RockBase-iot/NM-EPD-420/src/ui/epd_uc8179_420c.cpp

#include "epd_uc8179_420c.h"

static inline uint8_t remapPlaneData(uint8_t command, uint8_t data)
{
    return (command == 0x13) ? static_cast<uint8_t>(~data) : data;
}

GxEPD2_420c_NM_UC8179::GxEPD2_420c_NM_UC8179(int16_t cs, int16_t dc, int16_t rst, int16_t busy)
    : GxEPD2_EPD(cs, dc, rst, busy, LOW, 25000000, WIDTH, HEIGHT,
                 panel, hasColor, hasPartialUpdate, hasFastPartialUpdate)
{
}

void GxEPD2_420c_NM_UC8179::clearScreen(uint8_t value) { clearScreen(value, 0xFF); }

void GxEPD2_420c_NM_UC8179::clearScreen(uint8_t black_value, uint8_t color_value)
{
    writeScreenBuffer(black_value, color_value);
    refresh(false);
}

void GxEPD2_420c_NM_UC8179::writeScreenBuffer(uint8_t value) { writeScreenBuffer(value, 0xFF); }

void GxEPD2_420c_NM_UC8179::writeScreenBuffer(uint8_t black_value, uint8_t color_value)
{
    if (!_init_display_done) _InitDisplay();
    _writeScreenBuffer(0x10, black_value);
    _writeScreenBuffer(0x13, color_value);
    _initial_write = false;
}

void GxEPD2_420c_NM_UC8179::_writeScreenBuffer(uint8_t command, uint8_t value)
{
    _setPartialRamArea(0, 0, WIDTH, HEIGHT);
    _writeCommand(command);
    _startTransfer();
    uint8_t tx = remapPlaneData(command, value);
    for (uint32_t i = 0; i < uint32_t(WIDTH) * uint32_t(HEIGHT) / 8; i++) _transfer(tx);
    _endTransfer();
}

void GxEPD2_420c_NM_UC8179::writeImage(const uint8_t bitmap[], int16_t x, int16_t y,
                                       int16_t w, int16_t h, bool invert, bool mirror_y, bool pgm)
{
    _writeScreenBuffer(0x13, 0xFF);
    _writeImage(0x10, bitmap, x, y, w, h, invert, mirror_y, pgm);
}

void GxEPD2_420c_NM_UC8179::_writeImage(uint8_t command, const uint8_t bitmap[],
                                        int16_t x, int16_t y, int16_t w, int16_t h,
                                        bool invert, bool mirror_y, bool pgm)
{
    if (_initial_write) writeScreenBuffer();
    delay(1);
    uint16_t wb = (w + 7) / 8;
    x -= x % 8;
    w = wb * 8;
    int16_t x1 = x < 0 ? 0 : x;
    int16_t y1 = y < 0 ? 0 : y;
    int16_t w1 = x + w < int16_t(WIDTH) ? w : int16_t(WIDTH) - x;
    int16_t h1 = y + h < int16_t(HEIGHT) ? h : int16_t(HEIGHT) - y;
    int16_t dx = x1 - x;
    int16_t dy = y1 - y;
    w1 -= dx;
    h1 -= dy;
    if ((w1 <= 0) || (h1 <= 0)) return;
    if (!_init_display_done) _InitDisplay();
    _writeCommand(0x91);
    _setPartialRamArea(x1, y1, w1, h1);
    _writeCommand(command);
    _startTransfer();
    for (int16_t i = 0; i < h1; i++) {
        for (int16_t j = 0; j < w1 / 8; j++) {
            uint16_t idx = mirror_y
                ? j + dx / 8 + uint16_t((h - 1 - (i + dy))) * wb
                : j + dx / 8 + uint16_t(i + dy) * wb;
            uint8_t data = pgm ? pgm_read_byte(&bitmap[idx]) : bitmap[idx];
            if (invert) data = ~data;
            _transfer(remapPlaneData(command, data));
        }
    }
    _endTransfer();
    _writeCommand(0x92);
    delay(1);
}

void GxEPD2_420c_NM_UC8179::writeImagePart(const uint8_t bitmap[],
        int16_t x_part, int16_t y_part, int16_t w_bitmap, int16_t h_bitmap,
        int16_t x, int16_t y, int16_t w, int16_t h, bool invert, bool mirror_y, bool pgm)
{
    _writeImagePart(0x10, bitmap, x_part, y_part, w_bitmap, h_bitmap, x, y, w, h,
                    invert, mirror_y, pgm);
}

void GxEPD2_420c_NM_UC8179::_writeImagePart(uint8_t command, const uint8_t bitmap[],
        int16_t x_part, int16_t y_part, int16_t w_bitmap, int16_t h_bitmap,
        int16_t x, int16_t y, int16_t w, int16_t h, bool invert, bool mirror_y, bool pgm)
{
    if (_initial_write) writeScreenBuffer();
    delay(1);
    if ((w_bitmap < 0) || (h_bitmap < 0) || (w < 0) || (h < 0)) return;
    if ((x_part < 0) || (x_part >= w_bitmap)) return;
    if ((y_part < 0) || (y_part >= h_bitmap)) return;
    uint16_t wb_bitmap = (w_bitmap + 7) / 8;
    x_part -= x_part % 8;
    w = w_bitmap - x_part < w ? w_bitmap - x_part : w;
    h = h_bitmap - y_part < h ? h_bitmap - y_part : h;
    x -= x % 8;
    w = 8 * ((w + 7) / 8);
    int16_t x1 = x < 0 ? 0 : x;
    int16_t y1 = y < 0 ? 0 : y;
    int16_t w1 = x + w < int16_t(WIDTH) ? w : int16_t(WIDTH) - x;
    int16_t h1 = y + h < int16_t(HEIGHT) ? h : int16_t(HEIGHT) - y;
    int16_t dx = x1 - x;
    int16_t dy = y1 - y;
    w1 -= dx;
    h1 -= dy;
    if ((w1 <= 0) || (h1 <= 0)) return;
    if (!_init_display_done) _InitDisplay();
    _writeCommand(0x91);
    _setPartialRamArea(x1, y1, w1, h1);
    _writeCommand(command);
    _startTransfer();
    for (int16_t i = 0; i < h1; i++) {
        for (int16_t j = 0; j < w1 / 8; j++) {
            uint32_t idx = mirror_y
                ? x_part / 8 + j + dx / 8 + uint32_t((h_bitmap - 1 - (y_part + i + dy))) * wb_bitmap
                : x_part / 8 + j + dx / 8 + uint32_t(y_part + i + dy) * wb_bitmap;
            uint8_t data = pgm ? pgm_read_byte(&bitmap[idx]) : bitmap[idx];
            if (invert) data = ~data;
            _transfer(remapPlaneData(command, data));
        }
    }
    _endTransfer();
    _writeCommand(0x92);
    delay(1);
}

void GxEPD2_420c_NM_UC8179::writeImage(const uint8_t* black, const uint8_t* color,
        int16_t x, int16_t y, int16_t w, int16_t h, bool invert, bool mirror_y, bool pgm)
{
    if (black) _writeImage(0x10, black, x, y, w, h, invert, mirror_y, pgm);
    if (color) _writeImage(0x13, color, x, y, w, h, invert, mirror_y, pgm);
}

void GxEPD2_420c_NM_UC8179::writeImagePart(const uint8_t* black, const uint8_t* color,
        int16_t x_part, int16_t y_part, int16_t w_bitmap, int16_t h_bitmap,
        int16_t x, int16_t y, int16_t w, int16_t h, bool invert, bool mirror_y, bool pgm)
{
    if (black) _writeImagePart(0x10, black, x_part, y_part, w_bitmap, h_bitmap, x, y, w, h,
                               invert, mirror_y, pgm);
    if (color) _writeImagePart(0x13, color, x_part, y_part, w_bitmap, h_bitmap, x, y, w, h,
                               invert, mirror_y, pgm);
}

void GxEPD2_420c_NM_UC8179::writeNative(const uint8_t* data1, const uint8_t* data2,
        int16_t x, int16_t y, int16_t w, int16_t h, bool invert, bool mirror_y, bool pgm)
{
    (void)data2;
    if (data1) writeImage(data1, x, y, w, h, invert, mirror_y, pgm);
}

void GxEPD2_420c_NM_UC8179::drawImage(const uint8_t bitmap[], int16_t x, int16_t y,
                                      int16_t w, int16_t h, bool invert, bool mirror_y, bool pgm)
{
    writeImage(bitmap, x, y, w, h, invert, mirror_y, pgm);
    refresh(x, y, w, h);
}

void GxEPD2_420c_NM_UC8179::drawImagePart(const uint8_t bitmap[],
        int16_t x_part, int16_t y_part, int16_t w_bitmap, int16_t h_bitmap,
        int16_t x, int16_t y, int16_t w, int16_t h, bool invert, bool mirror_y, bool pgm)
{
    writeImagePart(bitmap, x_part, y_part, w_bitmap, h_bitmap, x, y, w, h, invert, mirror_y, pgm);
    refresh(x, y, w, h);
}

void GxEPD2_420c_NM_UC8179::drawImage(const uint8_t* black, const uint8_t* color,
        int16_t x, int16_t y, int16_t w, int16_t h, bool invert, bool mirror_y, bool pgm)
{
    writeImage(black, color, x, y, w, h, invert, mirror_y, pgm);
    refresh(x, y, w, h);
}

void GxEPD2_420c_NM_UC8179::drawImagePart(const uint8_t* black, const uint8_t* color,
        int16_t x_part, int16_t y_part, int16_t w_bitmap, int16_t h_bitmap,
        int16_t x, int16_t y, int16_t w, int16_t h, bool invert, bool mirror_y, bool pgm)
{
    writeImagePart(black, color, x_part, y_part, w_bitmap, h_bitmap, x, y, w, h,
                   invert, mirror_y, pgm);
    refresh(x, y, w, h);
}

void GxEPD2_420c_NM_UC8179::drawNative(const uint8_t* data1, const uint8_t* data2,
        int16_t x, int16_t y, int16_t w, int16_t h, bool invert, bool mirror_y, bool pgm)
{
    writeNative(data1, data2, x, y, w, h, invert, mirror_y, pgm);
    refresh(x, y, w, h);
}

void GxEPD2_420c_NM_UC8179::refresh(bool partial_update_mode)
{
    if (partial_update_mode) refresh(0, 0, WIDTH, HEIGHT);
    else _Update_Full();
}

void GxEPD2_420c_NM_UC8179::refresh(int16_t x, int16_t y, int16_t w, int16_t h)
{
    (void)x;
    (void)y;
    (void)w;
    (void)h;
    _Update_Full();
}

void GxEPD2_420c_NM_UC8179::powerOff() { _PowerOff(); }

void GxEPD2_420c_NM_UC8179::hibernate()
{
    _PowerOff();
    if (_rst >= 0) {
        _writeCommand(0x07);
        _writeData(0xA5);
        _hibernating = true;
        _init_display_done = false;
    }
}

void GxEPD2_420c_NM_UC8179::_setPartialRamArea(uint16_t x, uint16_t y, uint16_t w, uint16_t h)
{
    uint16_t xe = (x + w - 1) | 0x0007;
    uint16_t ye = y + h - 1;
    x &= 0xFFF8;
    _writeCommand(0x90);
    _writeData(x / 256);
    _writeData(x % 256);
    _writeData(xe / 256);
    _writeData(xe % 256);
    _writeData(y / 256);
    _writeData(y % 256);
    _writeData(ye / 256);
    _writeData(ye % 256);
    _writeData(0x00);
}

void GxEPD2_420c_NM_UC8179::_PowerOn()
{
    if (!_power_is_on) {
        _writeCommand(0x04);
        _waitWhileBusy("_PowerOn", power_on_time);
    }
    _power_is_on = true;
}

void GxEPD2_420c_NM_UC8179::_PowerOff()
{
    if (_power_is_on) {
        _writeCommand(0x02);
        _waitWhileBusy("_PowerOff", power_off_time);
        _power_is_on = false;
    }
}

void GxEPD2_420c_NM_UC8179::_InitDisplay()
{
    if (_hibernating) _reset();
    _writeCommand(0x01);
    _writeData(0x07);
    _writeData(0x07);
    _writeData(0x3f);
    _writeData(0x3f);
    _writeCommand(0x06);
    _writeData(0x17);
    _writeData(0x17);
    _writeData(0x28);
    _writeData(0x17);
    _writeCommand(0x00);
    _writeData(0x0f);
    _writeCommand(0x61);
    _writeData(WIDTH / 256);
    _writeData(WIDTH % 256);
    _writeData(HEIGHT / 256);
    _writeData(HEIGHT % 256);
    _writeCommand(0x15);
    _writeData(0x00);
    _writeCommand(0x50);
    _writeData(0x13);
    _writeData(0x07);
    _writeCommand(0x60);
    _writeData(0x22);
    _init_display_done = true;
}

void GxEPD2_420c_NM_UC8179::_Update_Full()
{
    _writeCommand(0x00);
    _writeData(0x0f);
    _writeCommand(0x50);
    _writeData(0x13);
    _writeData(0x07);
    _writeCommand(0xE0);
    _writeData(0x00);
    _writeCommand(0x41);
    _writeData(0x00);
    _PowerOn();
    _writeCommand(0x12);
    _waitWhileBusy("_Update_Full", full_refresh_time);
    _PowerOff();
}
